notAbhay321/Dual-power-supply/ki_cad_pcb_power_supply/power_supply.kicad_sch

## KiCad design ki_cad_pcb_power_supply/power_supply.kicad_sch (2026-06-29)

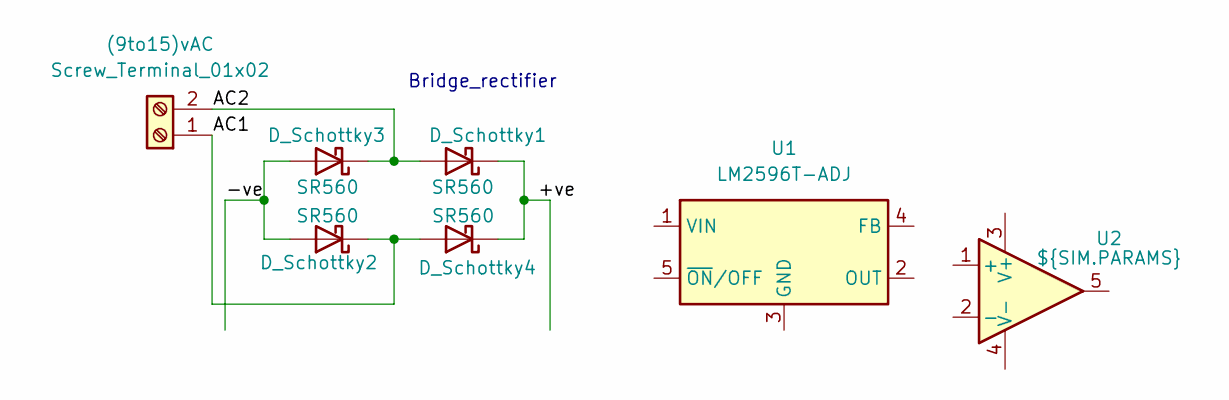
[picture p5: schematic power_supply.kicad_sch]

Parts:
(9to15)vAC: Screw_Terminal_01x02
D_Schottky1, D_Schottky2, D_Schottky3, D_Schottky4: SR560
U1: LM2596T-ADJ; TO-220-5_P3.4x3.7mm_StaggerOdd_Lead3.8mm_Vertical
U2: ${SIM.PARAMS}

Connections:
+ve: D_Schottky1.1 (K), D_Schottky4.1 (K)
-ve: D_Schottky2.2 (A), D_Schottky3.2 (A)
AC1: (9to15)vAC.1, D_Schottky2.1 (K), D_Schottky4.2 (A)
AC2: (9to15)vAC.2, D_Schottky1.2 (A), D_Schottky3.1 (K)

Notes on the sheet:
Bridge_rectifier
